douardda/ESP32-GPIB-pcb/assets/IMG_20220312_161600.jpg

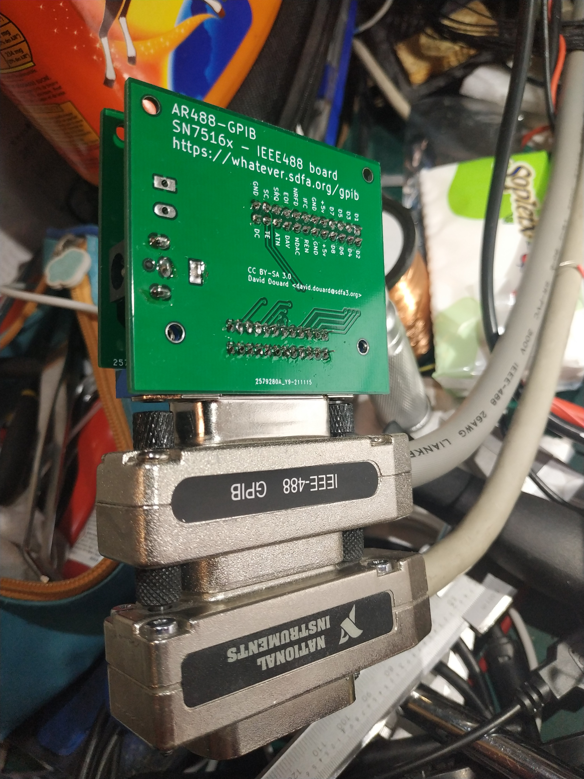
assets/IMG_20220312_161600.jpg
